arrowtype/80forty/artwork/80forty-pcb-art-2023_11_05.png

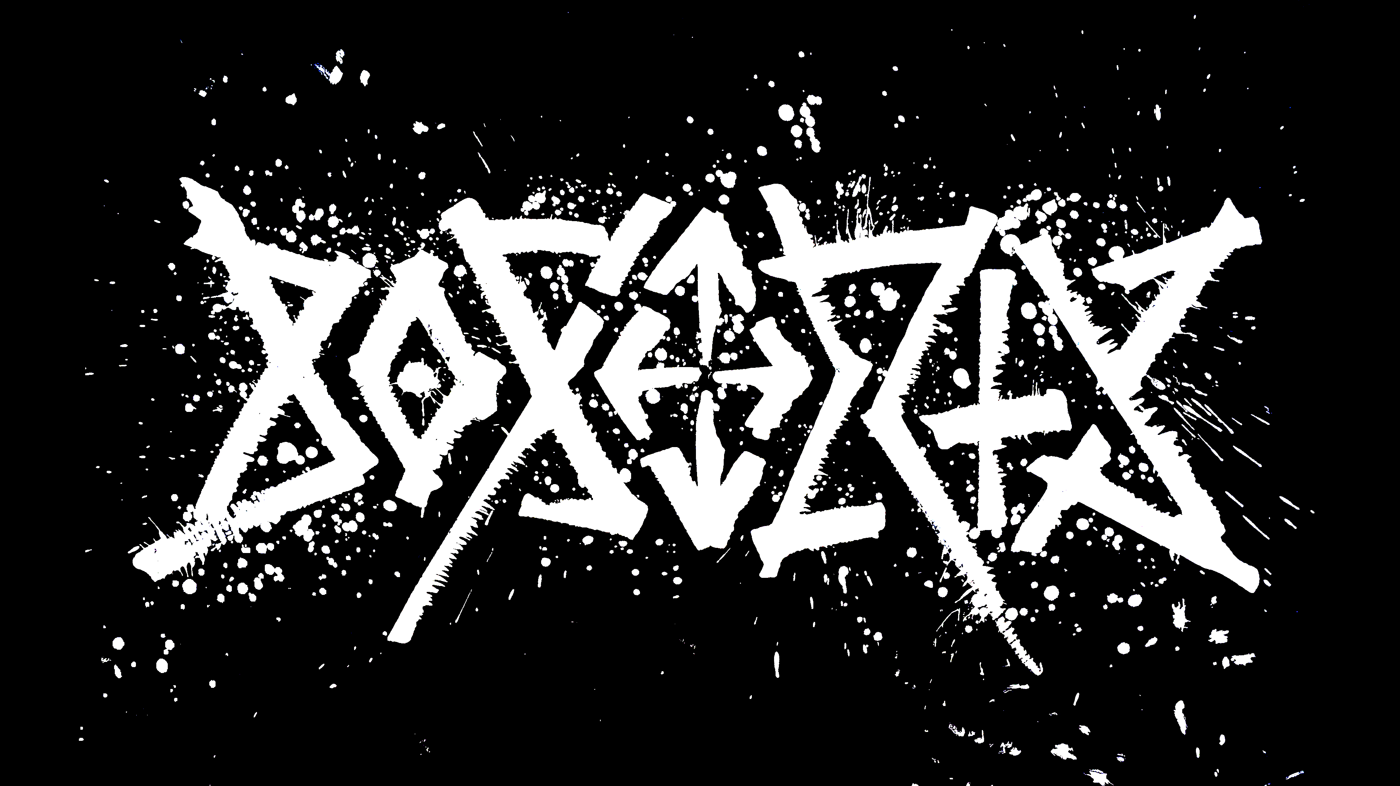
artwork/80forty-pcb-art-2023_11_05.png
